intositeme/kb-split/kb-split.jpg

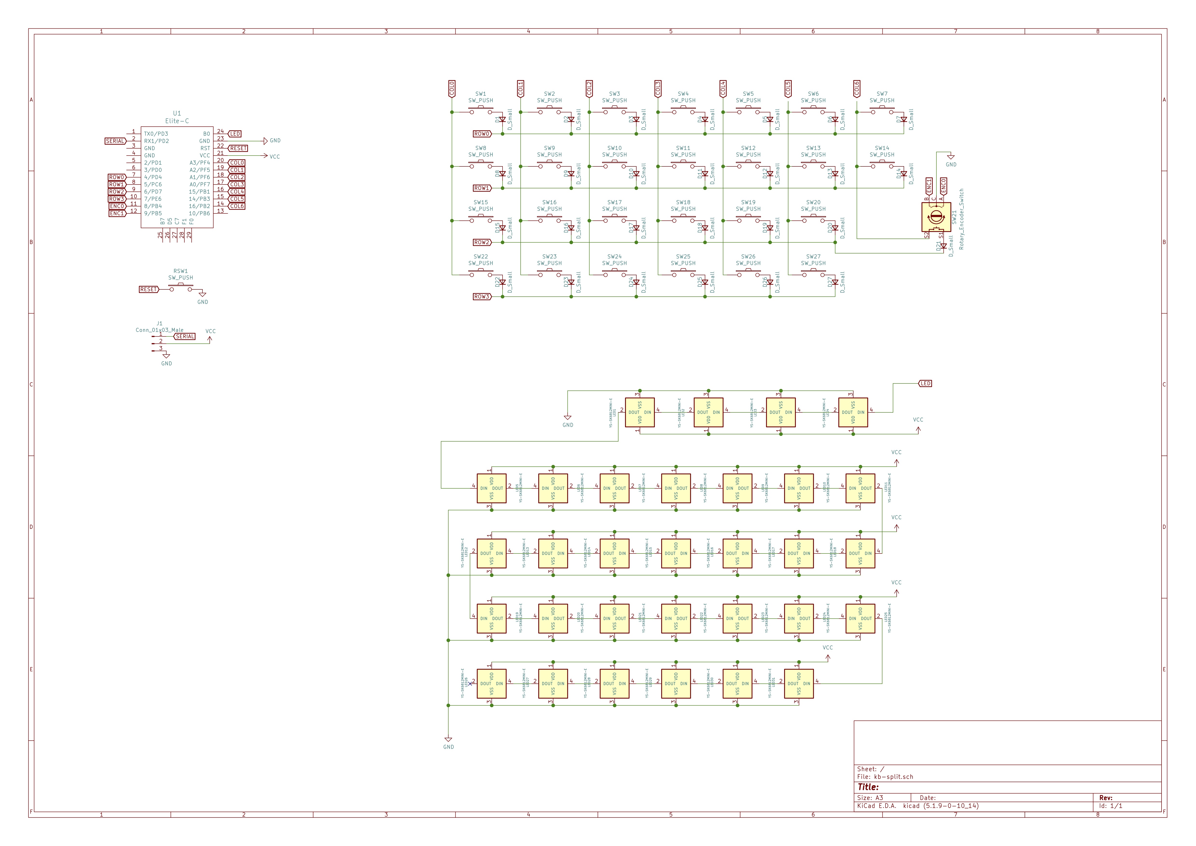
kb-split.jpg
